xlceor/Adaptative_robotic_gripper-for-EMG/mechanical/body/gripper_bar/v0.1/body.step

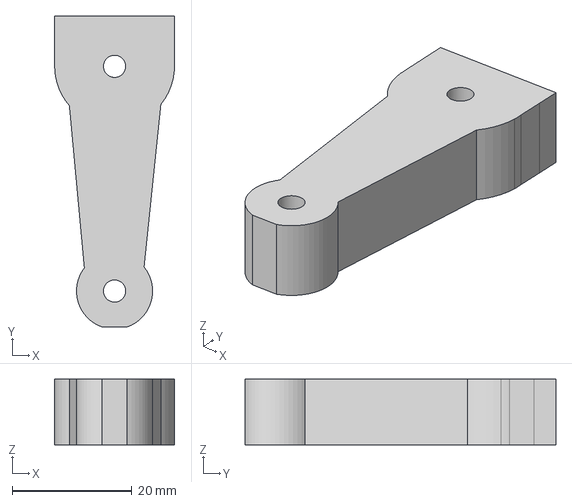
[picture p16: CAD file, 2026-02-06, an earlier design]
mechanical/body/gripper_bar/v0.1/body.step
20.0 x 51.9 x 11.0 mm
