xlceor/Adaptative_robotic_gripper-for-EMG/mechanical/body/linkage_bars/geared_bar/v1.1/gear_servo.stl

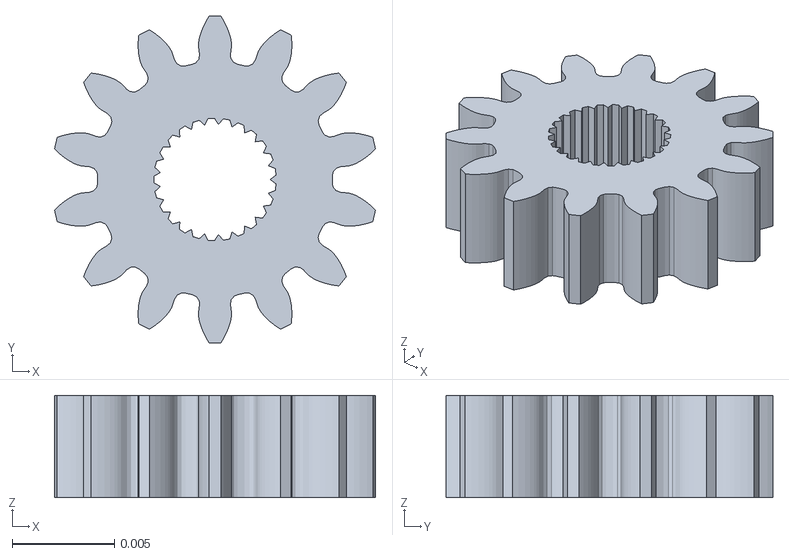
[picture p17: CAD file, 2026-02-09, an earlier design]
mechanical/body/linkage_bars/geared_bar/v1.1/gear_servo.stl
0.0157 x 0.016 x 0.005
